marcelobarrosufu/brewbuddy/brew_buddy/Inc/bb_locale_ENUS.h

/*
  BrewBuddy by Marcelo Barros de Almeida is licensed under a
  Creative Commons Attribution-NonCommercial-ShareAlike 4.0 International License.

  For commercial usage, please contact the author via marcelobarrosalmeida@gmail.com
*/

#ifndef BB_LOCALE_PTBR_H_
#define BB_LOCALE_PTBR_H_

#define BB_VERSION                  "1.0"
#define BB_TEMP_UNIT_IS_CELSIUS     0
#define BB_TEMP_UNIT_LABEL          "F"
#define BB_SPLASH1                  "BREW"
#define BB_SPLASH2                  "BUDDY"
#define BB_SIMUL                    "SIMULATION"
#define BB_FCTINIT                  "FACT. INIT"
#define BB_TEMP_LABEL               "TEMPERATURE"
#define BB_DURATION_UNITY           "m"
#define BB_DURATION_LABEL           "DURATION"
#define BB_NOT_IMPL                 "NOT IMPLEMENTED"
#define BB_OP_TEMP_LABEL            "THERMOMETER"
#define BB_OP_AUTO_MASH_LABEL       "MOISTURE"
#define BB_OP_AUTO_BOIL_LABEL       "BOILING"
#define BB_TIME_LABEL               "TIME"
#define BB_OP_AUTO_MASH_TITLE_LABEL "STEP CONFIG."
#define BB_AUTO_MASH_TITLE_LABEL    "STEP   TEMP  DURATION"
#define BB_AUTO_HEATING_LABEL       "(Ht)"
#define BB_AUTO_MESH_END_LABEL      "MASHING FINISHED"
#define BB_AUTO_BOIL_END_LABEL      "BOILING FINISHED"
#define BB_PAUSED_LABEL             "PAUSED "
#define BB_OP_AUTO_BOIL_TITLE_LABEL "BOILING CONFIG."
#define BB_OP_AUTO_BOIL_HOP_TITLE_LABEL "HOP CONFIG."
#define BB_AUTO_BOILH_TITLE_LABEL    "DURATION         NEXT"
#define BB_AUTO_BOILHA_TITLE_LABEL   "DURATION      ADD HOP"
//                                    12/90m            12m
#define BB_AUTO_BOIL_TITLE_LABEL     "DURATION"


#endif /* BB_LOCALE_PTBR_H_ */
