marcelobarrosufu/brewbuddy/brew_buddy/Src/lmt86.c

/*
  BrewBuddy by Marcelo Barros de Almeida is licensed under a
  Creative Commons Attribution-NonCommercial-ShareAlike 4.0 International License.

  For commercial usage, please contact the author via marcelobarrosalmeida@gmail.com
*/

#include <stdint.h>
#include "bb_locale.h"
#include "lmt86.h"

typedef struct lmt86_table_row_s
{
	int8_t temp_c;
	uint16_t mv_1d;
} __attribute__((packed)) lmt86_table_row_t;

const lmt86_table_row_t lmt86_table[]  =
{
	// temp C, mV*10
	{ -5, 21540 },
	{ -4, 21430 },
	{ -3, 21320 },
	{ -2, 21220 },
	{ -1, 21110 },
	{ 0, 21000 },
	{ 1, 20890 },
	{ 2, 20790 },
	{ 3, 20680 },
	{ 4, 20570 },
	{ 5, 20470 },
	{ 6, 20360 },
	{ 7, 20250 },
	{ 8, 20140 },
	{ 9, 20040 },
	{ 10, 19930 },
	{ 11, 19820 },
	{ 12, 19710 },
	{ 13, 19610 },
	{ 14, 19500 },
	{ 15, 19390 },
	{ 16, 19280 },
	{ 17, 19180 },
	{ 18, 19070 },
	{ 19, 18960 },
	{ 20, 18850 },
	{ 21, 18740 },
	{ 22, 18640 },
	{ 23, 18530 },
	{ 24, 18420 },
	{ 25, 18310 },
	{ 26, 18200 },
	{ 27, 18100 },
	{ 28, 17990 },
	{ 29, 17880 },
	{ 30, 17770 },
	{ 31, 17660 },
	{ 32, 17560 },
	{ 33, 17450 },
	{ 34, 17340 },
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
};

const uint16_t lmt86_table_size = sizeof(lmt86_table)/sizeof(lmt86_table[0]);

int16_t lmt86_find_temp_idx(uint32_t mv_id)
{
	uint16_t mid = 0;
	int16_t upper = lmt86_table_size - 1;
	int16_t lower = 0;

	while(lower <= upper)
	{
		mid = lower + (upper - lower) / 2;

		if(lmt86_table[mid].mv_1d == mv_id)
		{
			break;
		}
		else if(mv_id < lmt86_table[mid].mv_1d)
		{
			lower = mid + 1;
		}
		else
		{
			upper = mid - 1;
		}
	}

	return mid;
}

int32_t lmt86_interpolate_1d(int16_t idx, int32_t mv_1d)
{
	if(((idx <= 0)                      && (mv_1d > lmt86_table[idx].mv_1d)) ||
	   ((idx >= (lmt86_table_size - 1)) && (mv_1d < lmt86_table[idx].mv_1d)))
	{
		return lmt86_table[idx].temp_c;
	}
	else
	{
		volatile int32_t t1, t2, v1, v2, r, dt, dv;

		if(mv_1d < lmt86_table[idx].mv_1d)
		{
			t2 = lmt86_table[idx+1].temp_c;
			t1 = lmt86_table[idx].temp_c;
			v2 = lmt86_table[idx+1].mv_1d;
			v1 = lmt86_table[idx].mv_1d;

		}
		else
		{
			t2 = lmt86_table[idx].temp_c;
			t1 = lmt86_table[idx-1].temp_c;
			v2 = lmt86_table[idx].mv_1d;
			v1 = lmt86_table[idx-1].mv_1d;
		}

		dt = t2 - t1;
		dv = v2 - v1;

		r = ((dt*mv_1d + t1*dv - dt*v1)*100) / dv;
		r = r / 10;

		return r;
	}
}

int32_t lmt86_locale_conv_temp(int32_t c1d)
{
#if BB_TEMP_UNIT_IS_CELSIUS == 1
	return c1d;
#else
	return ((c1d*18) + 3200)/10;
#endif
}

int32_t lmt86_conv_temp_1d(uint32_t adc_val, uint32_t adc_steps, uint32_t vref_mv)
{
	int16_t idx;
	volatile uint32_t mv_1d = ((adc_val*vref_mv*100)/adc_steps)/10;
	idx = lmt86_find_temp_idx(mv_1d);

	if(idx == -1)
		return lmt86_locale_conv_temp(lmt86_table[0].temp_c*10); // error, minimum scale value
	else if(lmt86_table[idx].mv_1d == mv_1d) // exact
		return lmt86_locale_conv_temp(lmt86_table[idx].temp_c*10);
	else
		return lmt86_locale_conv_temp(lmt86_interpolate_1d(idx,mv_1d));
}
