marcelobarrosufu/brewbuddy/brew_buddy/Inc/bb_locale_PTBR.h

/*
  BrewBuddy by Marcelo Barros de Almeida is licensed under a
  Creative Commons Attribution-NonCommercial-ShareAlike 4.0 International License.

  For commercial usage, please contact the author via marcelobarrosalmeida@gmail.com
*/

#ifndef BB_LOCALE_PTBR_H_
#define BB_LOCALE_PTBR_H_

#define BB_VERSION                  "1.0"
#define BB_TEMP_UNIT_IS_CELSIUS     1
#define BB_TEMP_UNIT_LABEL          "C"
#define BB_SPLASH1                  "BREW"
#define BB_SPLASH2                  "BUDDY"
#define BB_SIMUL                    "SIMULACAO"
#define BB_FCTINIT                  "INIC. DE FABRICA"
#define BB_TEMP_LABEL               "TEMPERATURA"
#define BB_DURATION_UNITY           "m"
#define BB_DURATION_LABEL           "DURACAO"
#define BB_NOT_IMPL                 "NAO IMPLEMENTADO"
#define BB_OP_TEMP_LABEL            "TERMOMETRO"
#define BB_OP_AUTO_MASH_LABEL       "MOSTURA"
#define BB_OP_AUTO_BOIL_LABEL       "FERVURA"
#define BB_TIME_LABEL               "TEMPO"
#define BB_OP_AUTO_MASH_TITLE_LABEL "CONFIG. RAMPA"
#define BB_AUTO_MASH_TITLE_LABEL    "RAMPA  TEMP  DURACAO "
#define BB_AUTO_HEATING_LABEL       "(Aq)"
#define BB_AUTO_MESH_END_LABEL      "BRASSAGEM FINALIZADA"
#define BB_AUTO_BOIL_END_LABEL      "FERVURA FINALIZADA"
#define BB_PAUSED_LABEL             "PAUSADO"
#define BB_OP_AUTO_BOIL_TITLE_LABEL "CONFIG. FERVURA"
#define BB_OP_AUTO_BOIL_HOP_TITLE_LABEL "CONFIG. LUPULO"
#define BB_AUTO_BOILH_TITLE_LABEL    "DURACAO       PROXIMO"
#define BB_AUTO_BOILHA_TITLE_LABEL   "DURACAO   ADC. LUPULO"
//                                    12/90m            12m
#define BB_AUTO_BOIL_TITLE_LABEL     "DURACAO"


#endif /* BB_LOCALE_PTBR_H_ */
